dren-dk/LEDstrip/hardware/ledctrl.sch

## KiCad design hardware/ledctrl.sch (2013-02-27)

Schematic: ledctrl.sch

Parts:
CON1: ISP; AVR-ISP-6
D1: LED
IC1: PCA9685
IC2: ATMEGA328P-A; TQFP32
JP1: a5
JP2: a4
JP3: a3
JP4: a2
JP5: a1
JP6: a0
P1: rgb0
P2: rgb1
P3: rgb2
P4: rgb3
P5: rgb4
P6: led
P7: rgbw
P8, P11: power
P9: gpio
P10: FTDI
P12, P14: i2c
P13: nRF24L01+
P15, P16, P17, P18, P19, P20, P21, P22: CONN_1
Q1, Q2, Q3, Q4, Q5, Q6, Q7, Q8, Q9, Q10, Q11, Q12, Q13, Q14, Q15, Q16, Q17, Q18, Q19, Q20: IRLTS6242
R1: 270R
R2, R3, R4: 10k

Notes on the sheet:
CSN
Note: Only fit pullups on one PCB of the bus
