dren-dk/LEDstrip/hardware/psu.sch

## KiCad design hardware/psu.sch (2013-02-27)

Schematic: psu.sch

Parts:
C1, C2, C3: 100nF
C21: 10uF/35V
C22, C23: 220uF/35V
C24: 4.7uF/16V
C25: 82pF
D5: SK 34
L5: 330uH
R13: 0R22
R14: 18k
R15: 11k
U5: MC34063

Notes on the sheet:
Distributed decoupling caps
